marcoallegretti/Glacial-Reverb/eurorack/dsp/Filter2Poles.hpp

/*****************************************************************************

     Filter2Poles.hpp (local copy)

*Tab=3***********************************************************************/

#pragma once

/*\\ INCLUDE FILES \\\\*/

namespace dsp
{

/*\\ PUBLIC \\\\*/

/*
==============================================================================
Name : process
==============================================================================
*/

inline float Filter2Poles::process (float x)
{
   const int alt_pos = 1 - _mem_pos;
   const float y
      = _z_eq_b [0] * x
      + (_z_eq_b [1] * _mem_x [_mem_pos] + _z_eq_b [2] * _mem_x [alt_pos])
      - (_z_eq_a [1] * _mem_y [_mem_pos] + _z_eq_a [2] * _mem_y [alt_pos]);

   _mem_x [alt_pos] = x;
   _mem_y [alt_pos] = y;
   _mem_pos = alt_pos;

   return y;
}

/*\\ INTERNAL \\\\*/


/*\\ PROTECTED \\\\*/


/*\\ PRIVATE \\\\*/

} // namespace dsp

/*\\ EOF \\\\*/
