marcoallegretti/Glacial-Reverb/eurorack/dsp/GainRamp.cpp

/*****************************************************************************

     GainRamp.cpp (local copy)

*Tab=3***********************************************************************/

/*\\ INCLUDE FILES \\\\*/

#include "GainRamp.h"

namespace dsp
{

/*\\ PUBLIC \\\\*/

/*
==============================================================================
Name : process
==============================================================================
*/

void  GainRamp::process ()
{
   constexpr float step = 1.f / 256.f;

   if (_cur < target)
   {
      _cur += step;
      if (_cur > target) _cur = target;
   }
   else if (_cur > target)
   {
      _cur -= step;
      if (_cur < target) _cur = target;
   }
}

/*\\ INTERNAL \\\\*/


/*\\ PROTECTED \\\\*/


/*\\ PRIVATE \\\\*/

} // namespace dsp

/*\\ EOF \\\\*/
