marcoallegretti/Glacial-Reverb/eurorack/dsp/GainRamp.h

/*****************************************************************************

     GainRamp.h (local copy)

*Tab=3***********************************************************************/

#pragma once

/*\\ INCLUDE FILES \\\\*/

namespace dsp
{

class GainRamp
{

/*\\ PUBLIC \\\\*/

public:
               GainRamp () = default;
   /*virtual*/ ~GainRamp () = default;

   float       target = 0.f;

   void        process ();
   inline      operator float () const;

/*\\ INTERNAL \\\\*/


/*\\ PROTECTED \\\\*/

protected:


/*\\ PRIVATE \\\\*/

private:
   float       _cur = 0.f;

/*\\ FORBIDDEN MEMBER FUNCTIONS \\\\*/

private:
               GainRamp (const GainRamp & rhs) = delete;
               GainRamp (GainRamp && rhs) = delete;
   GainRamp &  operator = (const GainRamp & rhs) = delete;
   GainRamp &  operator = (GainRamp && rhs) = delete;
   bool        operator == (const GainRamp & rhs) const = delete;
   bool        operator != (const GainRamp & rhs) const = delete;

}; // class GainRamp

} // namespace dsp

#include "GainRamp.hpp"

/*\\ EOF \\\\*/
