marcoallegretti/Glacial-Reverb/eurorack/dsp/GainRamp.hpp

/*****************************************************************************

     GainRamp.hpp (local copy)

*Tab=3***********************************************************************/

#pragma once

/*\\ INCLUDE FILES \\\\*/

namespace dsp
{

/*\\ PUBLIC \\\\*/

/*
==============================================================================
Name : operator float
==============================================================================
*/

inline GainRamp::operator float () const
{
   return _cur;
}

/*\\ INTERNAL \\\\*/


/*\\ PROTECTED \\\\*/


/*\\ PRIVATE \\\\*/

} // namespace dsp

/*\\ EOF \\\\*/
